oho66/exterior-shell-design/Design Files/Door Latch/CAD/0.25-20BoltRound.SLDPRT

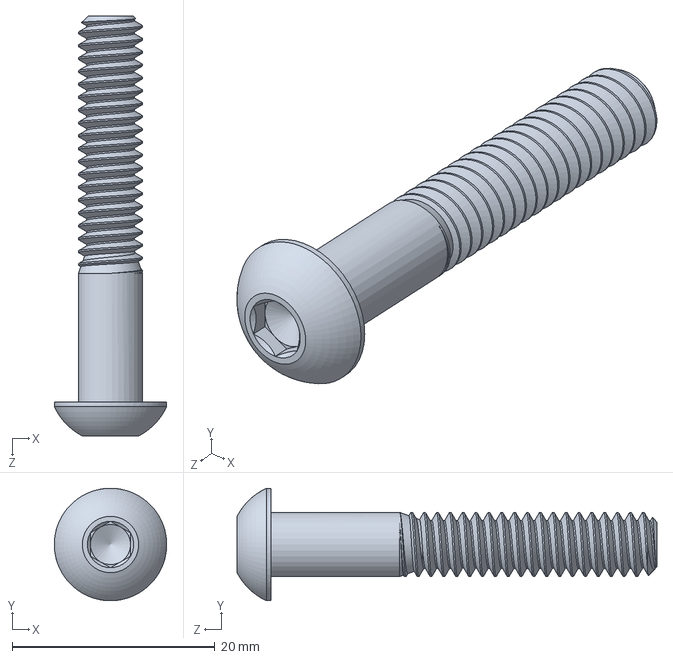
[picture p71: CAD file, 2023-07-19]
Design Files/Door Latch/CAD/0.25-20BoltRound.SLDPRT
11.1 x 11.1 x 41.5 mm
